badaboombox/SS-Handheld-Console/hardware/Comp Board/Audio.kicad_sch

## KiCad design hardware/Comp Board/Audio.kicad_sch (2026-07-28)

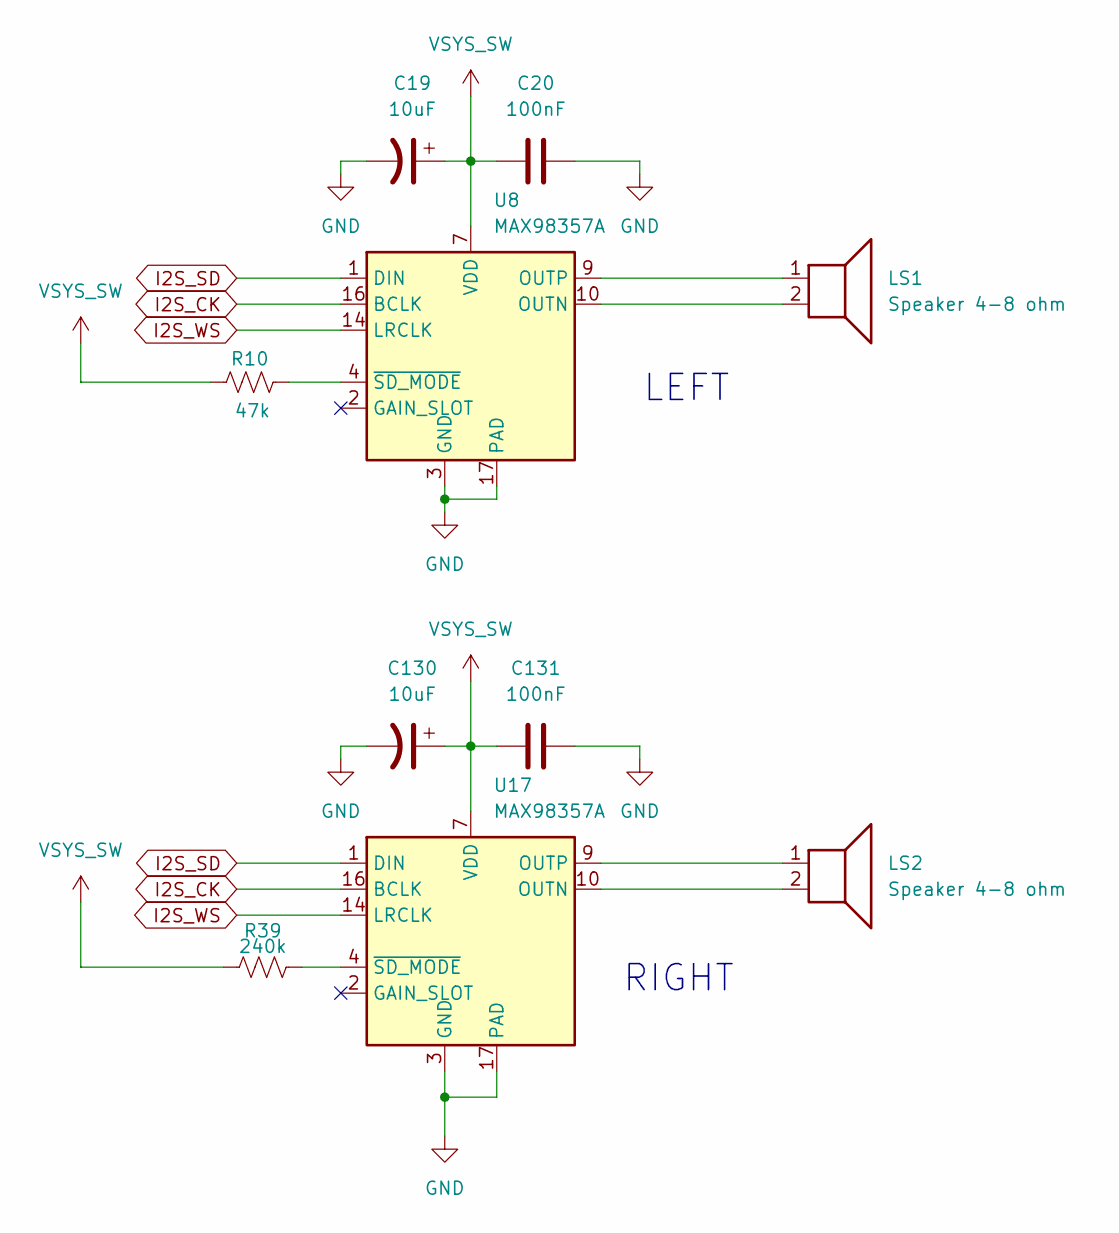
[picture p26: schematic Audio.kicad_sch]

Parts:
C19, C130: 10uF; C_0805_2012Metric
C20, C131: 100nF; C_0402_1005Metric
LS1, LS2: Speaker 4-8 ohm; TE_440054-2_1x02_P2.00mm_Vertical
R10: 47k; R_0402_1005Metric
R39: 240k; R_0402_1005Metric
U8, U17: MAX98357A; TQFN-16-1EP_3x3mm_P0.5mm_EP1.23x1.23mm

Connections:
GND: C19.2, C20.1, C130.2, C131.1, U8.3 (GND), U8.11 (GND), U8.15 (GND), U8.17 (PAD), U17.3 (GND), U17.11 (GND), U17.15 (GND), U17.17 (PAD)
I2S_CK: U8.16 (BCLK), U17.16 (BCLK)
I2S_SD: U8.1 (DIN), U17.1 (DIN)
I2S_WS: U8.14 (LRCLK), U17.14 (LRCLK)
unnamed: LS1.1, U8.9 (OUTP)
unnamed: LS1.2, U8.10 (OUTN)
unnamed: LS2.1, U17.9 (OUTP)
unnamed: LS2.2, U17.10 (OUTN)
unnamed: R10.2, U8.4 (~SD_MODE)
unnamed: R39.2, U17.4 (~SD_MODE)
VSYS_SW: C19.1, C20.2, C130.1, C131.2, R10.1, R39.1, U8.7 (VDD), U8.8 (VDD), U17.7 (VDD), U17.8 (VDD)

Notes on the sheet:
RIGHT
LEFT
