badaboombox/SS-Handheld-Console/hardware/Comp Board/CPU_CLK.kicad_sch

## KiCad design hardware/Comp Board/CPU_CLK.kicad_sch (2026-07-28)

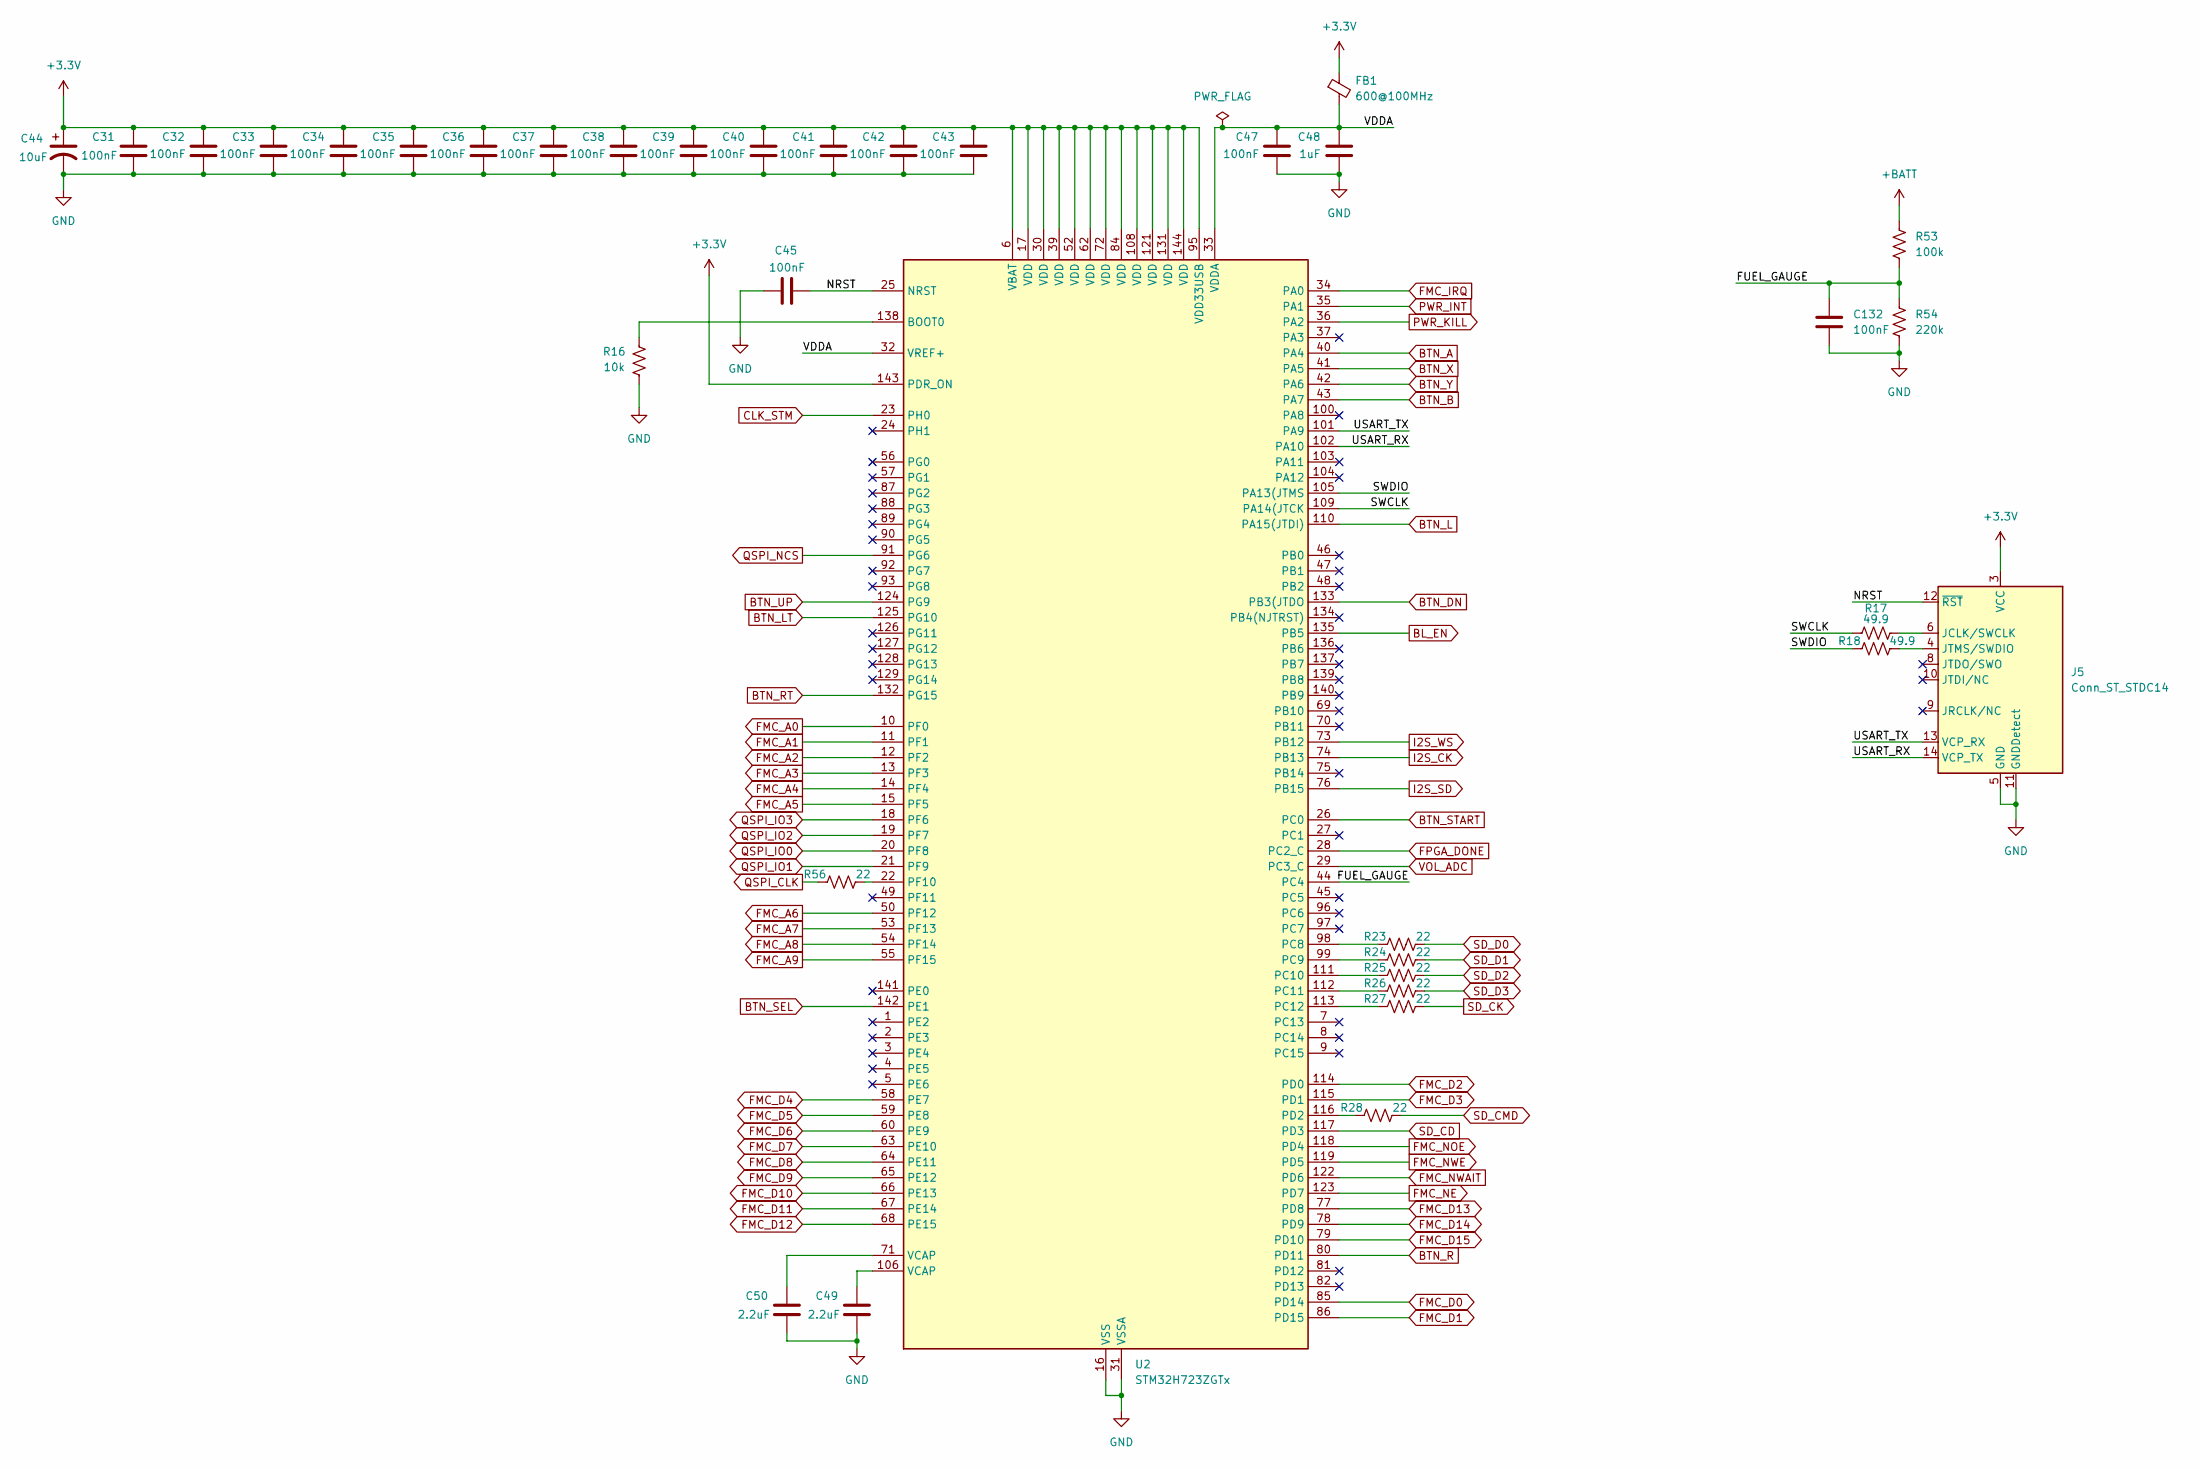
[picture p27: schematic CPU_CLK.kicad_sch]

Parts:
C31, C32, C33, C34, C35, C36, C37, C38, C39, C40, C41, C42, C43, C45, C47, C132: 100nF; C_0402_1005Metric
C44: 10uF; C_0805_2012Metric
C48: 1uF; C_0603_1608Metric
C49, C50: 2.2uF; C_0603_1608Metric
FB1: 600@100MHz; L_0805_2012Metric
J5: Conn_ST_STDC14; PinHeader_2x07_P1.27mm_Vertical
R16: 10k; R_0402_1005Metric
R17, R18: 49.9; R_0402_1005Metric
R23, R24, R25, R26, R27, R28, R56: 22; R_0402_1005Metric
R53: 100k; R_0402_1005Metric
R54: 220k; R_0402_1005Metric
U2: STM32H723ZGTx; LQFP-144_20x20mm_P0.5mm

Connections:
+3.3V: C31.1, C32.1, C33.1, C34.1, C35.1, C36.1, C37.1, C38.1, C39.1, C40.1, C41.1, C42.1, C43.1, C44.1, FB1.1, J5.3 (VCC), U2.6 (VBAT), U2.17 (VDD), U2.30 (VDD), U2.39 (VDD), U2.52 (VDD), U2.62 (VDD), U2.72 (VDD), U2.84 (VDD), U2.95 (VDD33USB), U2.108 (VDD), U2.121 (VDD), U2.131 (VDD), U2.143 (PDR_ON), U2.144 (VDD)
+BATT: R53.1
BL_EN: U2.135 (PB5)
BTN_A: U2.40 (PA4)
BTN_B: U2.43 (PA7)
BTN_DN: U2.133 (PB3(JTDO)
BTN_L: U2.110 (PA15(JTDI))
BTN_LT: U2.125 (PG10)
BTN_R: U2.80 (PD11)
BTN_RT: U2.132 (PG15)
BTN_SEL: U2.142 (PE1)
BTN_START: U2.26 (PC0)
BTN_UP: U2.124 (PG9)
BTN_X: U2.41 (PA5)
BTN_Y: U2.42 (PA6)
CLK_STM: U2.23 (PH0)
FMC_A0: U2.10 (PF0)
FMC_A1: U2.11 (PF1)
FMC_A2: U2.12 (PF2)
FMC_A3: U2.13 (PF3)
FMC_A4: U2.14 (PF4)
FMC_A5: U2.15 (PF5)
FMC_A6: U2.50 (PF12)
FMC_A7: U2.53 (PF13)
FMC_A8: U2.54 (PF14)
FMC_A9: U2.55 (PF15)
FMC_D0: U2.85 (PD14)
FMC_D1: U2.86 (PD15)
FMC_D2: U2.114 (PD0)
FMC_D3: U2.115 (PD1)
FMC_D4: U2.58 (PE7)
FMC_D5: U2.59 (PE8)
FMC_D6: U2.60 (PE9)
FMC_D7: U2.63 (PE10)
FMC_D8: U2.64 (PE11)
FMC_D9: U2.65 (PE12)
FMC_D10: U2.66 (PE13)
FMC_D11: U2.67 (PE14)
FMC_D12: U2.68 (PE15)
FMC_D13: U2.77 (PD8)
FMC_D14: U2.78 (PD9)
FMC_D15: U2.79 (PD10)
FMC_IRQ: U2.34 (PA0)
FMC_NE: U2.123 (PD7)
FMC_NOE: U2.118 (PD4)
FMC_NWAIT: U2.122 (PD6)
FMC_NWE: U2.119 (PD5)
FPGA_DONE: U2.28 (PC2_C)
FUEL_GAUGE: C132.1, R53.2, R54.1, U2.44 (PC4)
GND: C31.2, C32.2, C33.2, C34.2, C35.2, C36.2, C37.2, C38.2, C39.2, C40.2, C41.2, C42.2, C43.2, C44.2, C45.1, C47.2, C48.2, C49.2, C50.2, C132.2, J5.5 (GND), J5.7 (GND), J5.11 (GNDDetect), R16.1, R54.2, U2.16 (VSS), U2.31 (VSSA), U2.38 (VSS), U2.51 (VSS), U2.61 (VSS), U2.83 (VSS), U2.94 (VSS), U2.107 (VSS), U2.120 (VSS), U2.130 (VSS)
I2S_CK: U2.74 (PB13)
I2S_SD: U2.76 (PB15)
I2S_WS: U2.73 (PB12)
NRST: C45.2, J5.12 (~RST), U2.25 (NRST)
unnamed: C49.1, U2.106 (VCAP)
unnamed: C50.1, U2.71 (VCAP)
unnamed: J5.4 (JTMS/SWDIO), R18.2
unnamed: J5.6 (JCLK/SWCLK), R17.2
unnamed: R16.2, U2.138 (BOOT0)
unnamed: R23.1, U2.98 (PC8)
unnamed: R24.1, U2.99 (PC9)
unnamed: R25.1, U2.111 (PC10)
unnamed: R26.1, U2.112 (PC11)
unnamed: R27.1, U2.113 (PC12)
unnamed: R28.1, U2.116 (PD2)
unnamed: R56.2, U2.22 (PF10)
PWR_INT: U2.35 (PA1)
PWR_KILL: U2.36 (PA2)
QSPI_CLK: R56.1
QSPI_IO0: U2.20 (PF8)
QSPI_IO1: U2.21 (PF9)
QSPI_IO2: U2.19 (PF7)
QSPI_IO3: U2.18 (PF6)
QSPI_NCS: U2.91 (PG6)
SD_CD: U2.117 (PD3)
SD_CK: R27.2
SD_CMD: R28.2
SD_D0: R23.2
SD_D1: R24.2
SD_D2: R25.2
SD_D3: R26.2
SWCLK: R17.1, U2.109 (PA14(JTCK)
SWDIO: R18.1, U2.105 (PA13(JTMS)
USART_RX: J5.14 (VCP_TX), U2.102 (PA10)
USART_TX: J5.13 (VCP_RX), U2.101 (PA9)
VDDA: C47.1, C48.1, FB1.2, U2.32 (VREF+), U2.33 (VDDA)
VOL_ADC: U2.29 (PC3_C)
