badaboombox/SS-Handheld-Console/hardware/Comp Board/FPGA_Core_Conf.kicad_sch

## KiCad design hardware/Comp Board/FPGA_Core_Conf.kicad_sch (2026-07-28)

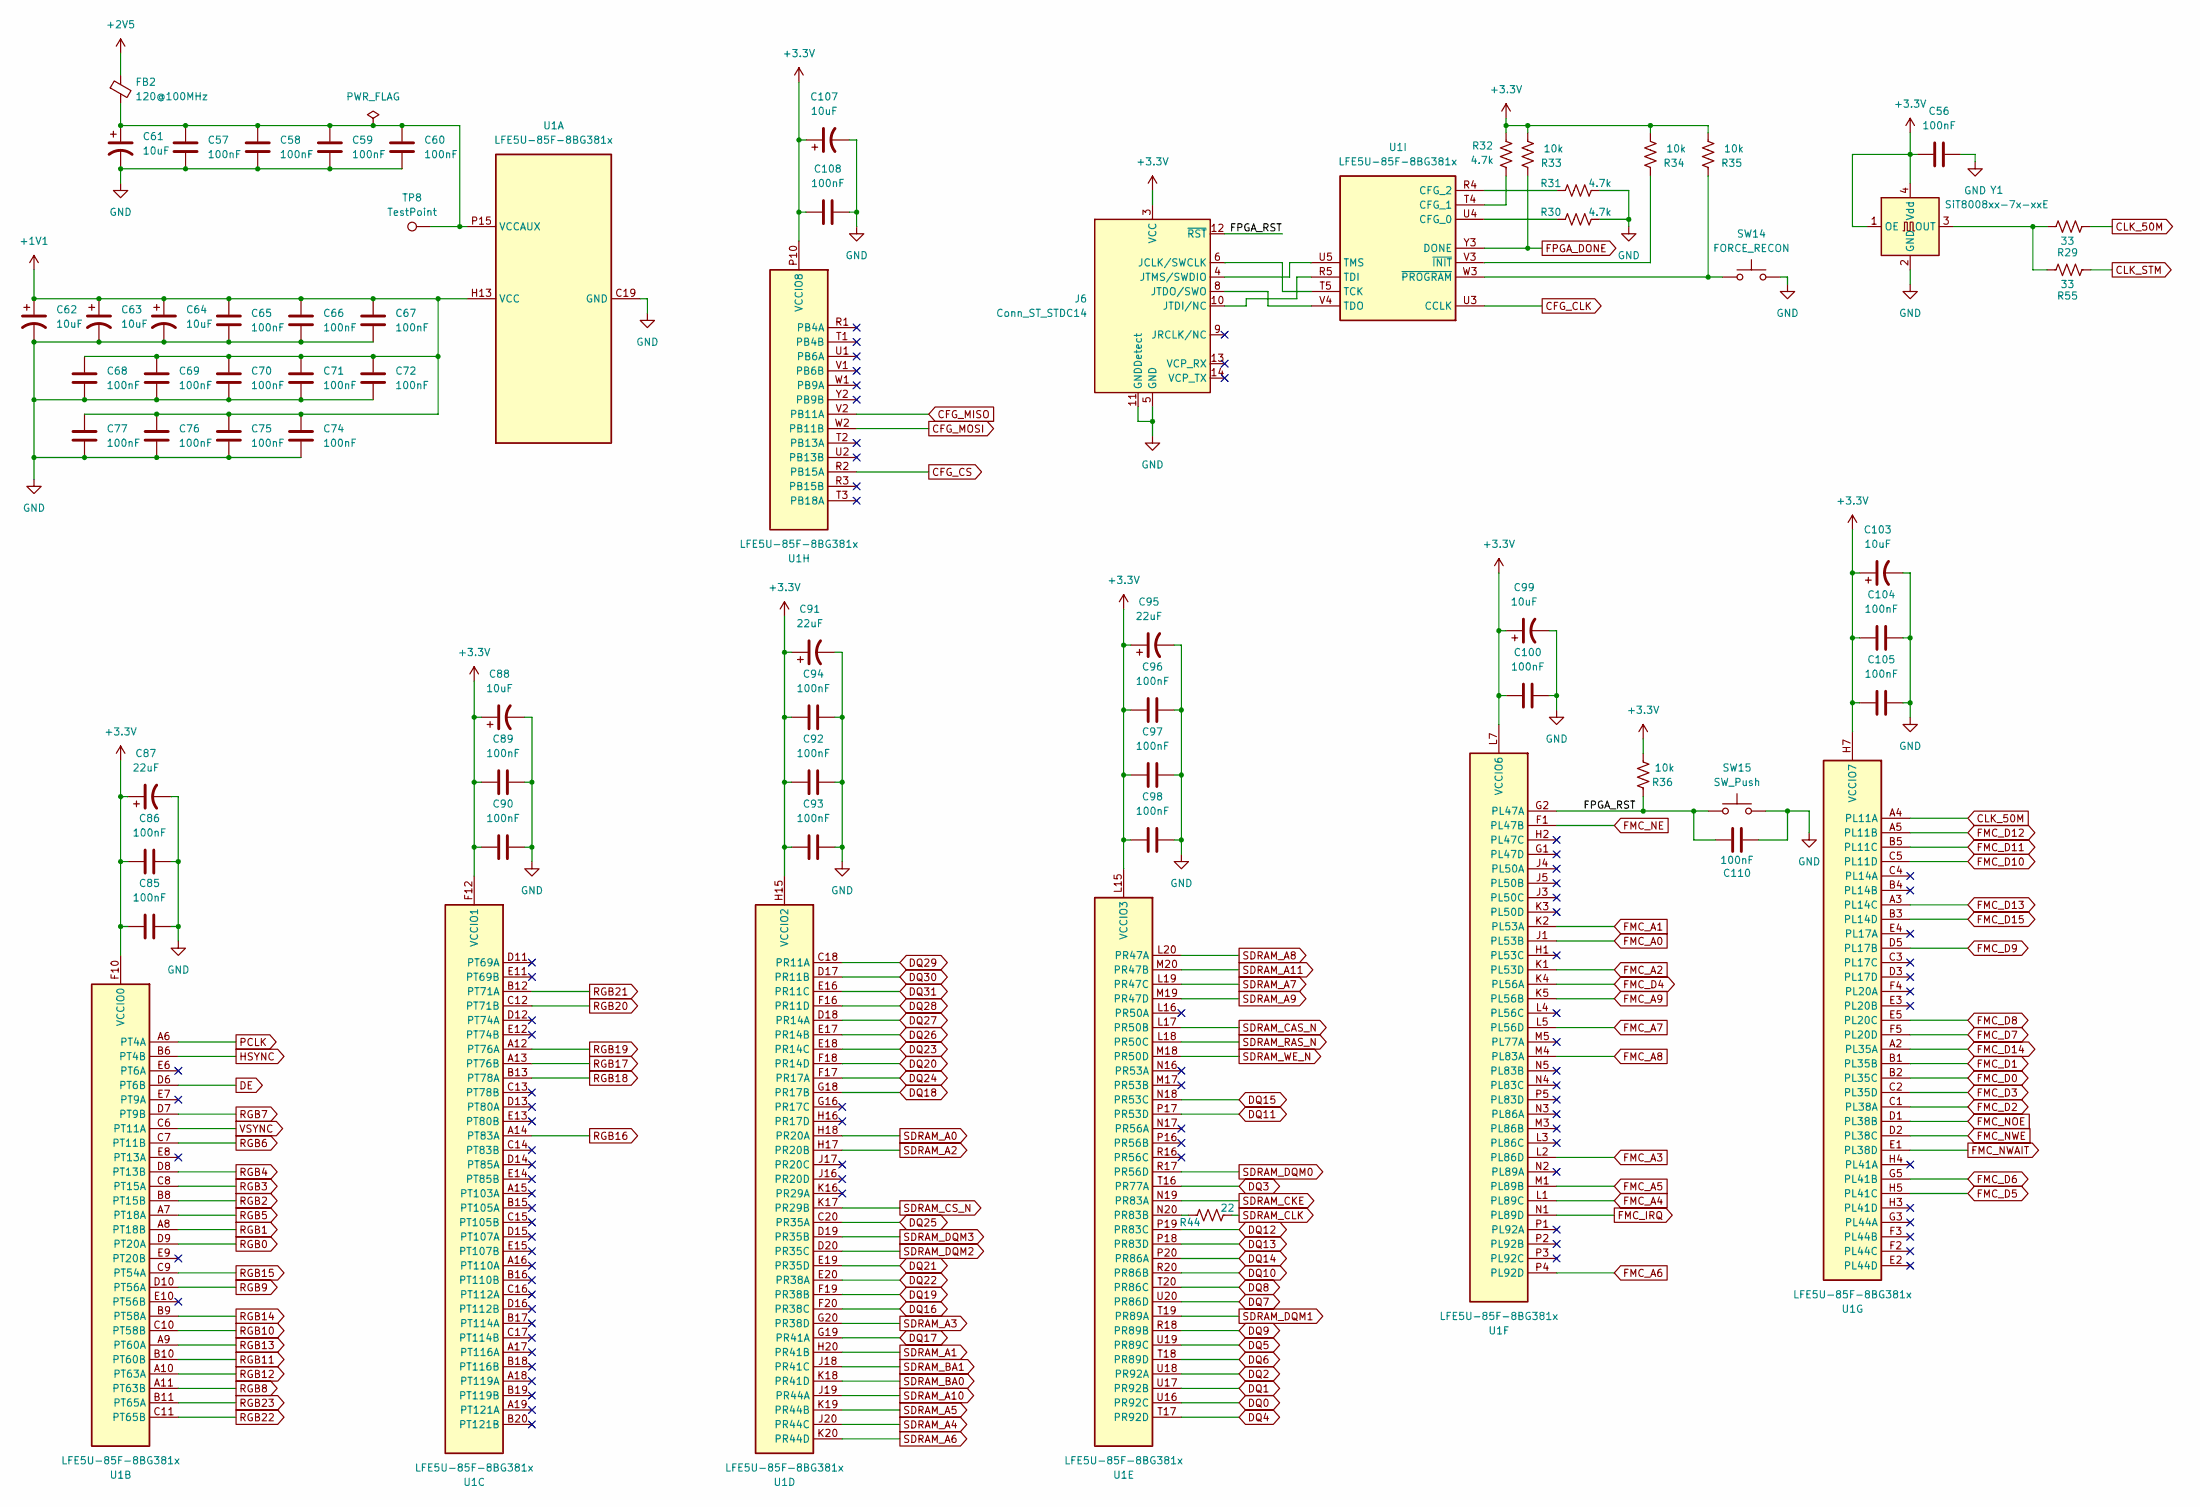
[picture p28: schematic FPGA_Core_Conf.kicad_sch]

Parts:
C56, C57, C58, C59, C60, C65, C66, C67, C68, C69, C70, C71, C72, C74, C75, C76, C77, C85, C86, C89, C90, C92, C93, C94, C96, C97, C98, C100, C104, C105, C108, C110: 100nF; C_0402_1005Metric
C61, C62, C63, C64, C88, C99, C103, C107: 10uF; C_0805_2012Metric
C87, C91, C95: 22uF; C_0805_2012Metric
FB2: 120@100MHz; L_0805_2012Metric
J6: Conn_ST_STDC14; PinHeader_2x07_P1.27mm_Vertical
R29, R55: 33; R_0402_1005Metric
R30, R31, R32: 4.7k; R_0402_1005Metric
R33, R34, R35, R36: 10k; R_0402_1005Metric
R44: 22; R_0402_1005Metric
SW14: FORCE_RECON; SW_Push_SPST_NO_Alps_SKRK
SW15: SW_Push; SW_Push_SPST_NO_Alps_SKRK
TP8: TestPoint; TestPoint_Pad_1.5x1.5mm
U1: LFE5U-85F-8BG381x; Lattice_caBGA-381_17x17mm_Layout20x20_P0.8mm
Y1: SiT8008xx-7x-xxE; Oscillator_SMD_SiT_PQFN-4Pin_2.0x1.6mm

Connections:
+1V1: C62.1, C63.1, C64.1, C65.2, C66.2, C67.2, C68.2, C69.2, C70.2, C71.2, C72.2, C74.2, C75.2, C76.2, C77.2, U1.H8 (VCC), U1.H9 (VCC), U1.H10 (VCC), U1.H11 (VCC), U1.H12 (VCC), U1.H13 (VCC), U1.J8 (VCC), U1.J13 (VCC), U1.K8 (VCC), U1.K13 (VCC), U1.L8 (VCC), U1.L13 (VCC), U1.M8 (VCC), U1.M13 (VCC), U1.N8 (VCC), U1.N9 (VCC), U1.N10 (VCC), U1.N11 (VCC), U1.N12 (VCC), U1.N13 (VCC)
+2V5: FB2.1
+3.3V: C56.1, C85.2, C86.2, C87.1, C88.1, C89.2, C90.2, C91.1, C92.2, C93.2, C94.2, C95.1, C96.2, C97.2, C98.2, C99.1, C100.2, C103.1, C104.2, C105.2, C107.1, C108.2, J6.3 (VCC), R32.1, R33.2, R34.2, R35.2, R36.2, U1.F9 (VCCIO0), U1.F10 (VCCIO0), U1.F11 (VCCIO1), U1.F12 (VCCIO1), U1.H6 (VCCIO7), U1.H7 (VCCIO7), U1.H14 (VCCIO2), U1.H15 (VCCIO2), U1.J6 (VCCIO7), U1.J15 (VCCIO2), U1.L6 (VCCIO6), U1.L7 (VCCIO6), U1.L14 (VCCIO3), U1.L15 (VCCIO3), U1.M6 (VCCIO6), U1.M15 (VCCIO3), U1.P9 (VCCIO8), U1.P10 (VCCIO8), Y1.1 (OE), Y1.4 (Vdd)
CFG_CLK: U1.U3 (CCLK)
CFG_CS: U1.R2 (PB15A)
CFG_MISO: U1.V2 (PB11A)
CFG_MOSI: U1.W2 (PB11B)
CLK_50M: R29.2, U1.A4 (PL11A)
CLK_STM: R55.2
DE: U1.D6 (PT6B)
DQ0: U1.U16 (PR92C)
DQ1: U1.U17 (PR92B)
DQ2: U1.U18 (PR92A)
DQ3: U1.T16 (PR77A)
DQ4: U1.T17 (PR92D)
DQ5: U1.U19 (PR89C)
DQ6: U1.T18 (PR89D)
DQ7: U1.U20 (PR86D)
DQ8: U1.T20 (PR86C)
DQ9: U1.R18 (PR89B)
DQ10: U1.R20 (PR86B)
DQ11: U1.P17 (PR53D)
DQ12: U1.P19 (PR83C)
DQ13: U1.P18 (PR83D)
DQ14: U1.P20 (PR86A)
DQ15: U1.N18 (PR53C)
DQ16: U1.F20 (PR38C)
DQ17: U1.G19 (PR41A)
DQ18: U1.G18 (PR17B)
DQ19: U1.F19 (PR38B)
DQ20: U1.F18 (PR14D)
DQ21: U1.E19 (PR35D)
DQ22: U1.E20 (PR38A)
DQ23: U1.E18 (PR14C)
DQ24: U1.F17 (PR17A)
DQ25: U1.C20 (PR35A)
DQ26: U1.E17 (PR14B)
DQ27: U1.D18 (PR14A)
DQ28: U1.F16 (PR11D)
DQ29: U1.C18 (PR11A)
DQ30: U1.D17 (PR11B)
DQ31: U1.E16 (PR11C)
FMC_A0: U1.J1 (PL53B)
FMC_A1: U1.K2 (PL53A)
FMC_A2: U1.K1 (PL53D)
FMC_A3: U1.L2 (PL86D)
FMC_A4: U1.L1 (PL89C)
FMC_A5: U1.M1 (PL89B)
FMC_A6: U1.P4 (PL92D)
FMC_A7: U1.L5 (PL56D)
FMC_A8: U1.M4 (PL83A)
FMC_A9: U1.K5 (PL56B)
FMC_D0: U1.B2 (PL35C)
FMC_D1: U1.B1 (PL35B)
FMC_D2: U1.C1 (PL38A)
FMC_D3: U1.C2 (PL35D)
FMC_D4: U1.K4 (PL56A)
FMC_D5: U1.H5 (PL41C)
FMC_D6: U1.G5 (PL41B)
FMC_D7: U1.F5 (PL20D)
FMC_D8: U1.E5 (PL20C)
FMC_D9: U1.D5 (PL17B)
FMC_D10: U1.C5 (PL11D)
FMC_D11: U1.B5 (PL11C)
FMC_D12: U1.A5 (PL11B)
FMC_D13: U1.A3 (PL14C)
FMC_D14: U1.A2 (PL35A)
FMC_D15: U1.B3 (PL14D)
FMC_IRQ: U1.N1 (PL89D)
FMC_NE: U1.F1 (PL47B)
FMC_NOE: U1.D1 (PL38B)
FMC_NWAIT: U1.E1 (PL38D)
FMC_NWE: U1.D2 (PL38C)
FPGA_DONE: R33.1, U1.Y3 (DONE)
FPGA_RST: C110.2, J6.12 (~RST), R36.1, SW15.1, U1.G2 (PL47A)
GND: C56.2, C57.1, C58.1, C59.1, C60.1, C61.2, C62.2, C63.2, C64.2, C65.1, C66.1, C67.1, C68.1, C69.1, C70.1, C71.1, C72.1, C74.1, C75.1, C76.1, C77.1, C85.1, C86.1, C87.2, C88.2, C89.1, C90.1, C91.2, C92.1, C93.1, C94.1, C95.2, C96.1, C97.1, C98.1, C99.2, C100.1, C103.2, C104.1, C105.1, C107.2, C108.1, C110.1, J6.5 (GND), J6.7 (GND), J6.11 (GNDDetect), R30.2, R31.2, SW14.2, SW15.2, U1.B7 (GND), U1.B14 (GND), U1.C19 (GND), U1.D4 (GND), U1.F7 (GND), U1.F8 (GND), U1.F13 (GND), U1.F14 (GND), U1.G4 (GND), U1.G6 (GND), U1.G7 (GND), U1.G8 (GND), U1.G9 (GND), U1.G10 (GND), U1.G11 (GND), U1.G12 (GND), U1.G13 (GND), U1.G14 (GND), U1.G15 (GND), U1.G17 (GND), U1.H19 (GND), U1.J2 (GND), U1.J7 (GND), U1.J9 (GND), U1.J10 (GND), U1.J11 (GND), U1.J12 (GND), U1.J14 (GND), U1.K6 (GND), U1.K7 (GND), U1.K9 (GND), U1.K10 (GND), U1.K11 (GND), U1.K12 (GND), U1.K14 (GND), U1.K15 (GND), U1.L9 (GND), U1.L10 (GND), U1.L11 (GND), U1.L12 (GND), U1.M2 (GND), U1.M7 (GND), U1.M9 (GND), U1.M10 (GND), U1.M11 (GND), U1.M12 (GND), U1.M14 (GND), U1.M16 (GND), U1.N6 (GND), U1.N7 (GND), U1.N14 (GND), U1.N15 (GND), U1.P7 (GND), U1.P8 (GND), U1.P11 (GND), U1.P12 (GND), U1.P13 (GND), U1.P14 (GND), U1.R19 (GND), U1.T6 (GND), U1.T7 (GND), U1.T8 (GND), U1.T9 (GND), U1.T10 (GND), U1.T11 (GND), U1.T12 (GND), U1.T13 (GND), U1.T14 (GND), U1.T15 (GND), U1.U6 (GND), U1.U7 (GND), U1.U8 (GND), U1.U9 (GND), U1.U10 (GND), U1.U11 (GND), U1.U12 (GND), U1.U13 (GND), U1.U14 (GND), U1.U15 (GND), U1.V5 (GND), U1.V6 (GND), U1.V7 (GND), U1.V8 (GND), U1.V9 (GND), U1.V10 (GND), U1.V11 (GND), U1.V12 (GND), U1.V13 (GND), U1.V14 (GND), U1.V15 (GND), U1.V16 (GND), U1.V17 (GND), U1.V18 (GND), U1.V19 (GND), U1.V20 (GND), U1.W6 (GND), U1.W7 (GND), U1.W12 (GND), U1.W15 (GND), U1.W16 (GND), U1.W19 (GND), U1.W20 (GND), U1.Y5 (GND), U1.Y6 (GND), U1.Y7 (GND), U1.Y8 (GND), U1.Y11 (GND), U1.Y12 (GND), U1.Y14 (GND), U1.Y15 (GND), U1.Y16 (GND), U1.Y17 (GND), U1.Y19 (GND), Y1.2 (GND)
HSYNC: U1.B6 (PT4B)
unnamed: C57.2, C58.2, C59.2, C60.2, C61.1, FB2.2, TP8.1, U1.F6 (VCCAUX), U1.F15 (VCCAUX), U1.P6 (VCCAUX), U1.P15 (VCCAUX)
unnamed: J6.4 (JTMS/SWDIO), U1.U5 (TMS)
unnamed: J6.6 (JCLK/SWCLK), U1.T5 (TCK)
unnamed: J6.8 (JTDO/SWO), U1.V4 (TDO)
unnamed: J6.10 (JTDI/NC), U1.R5 (TDI)
unnamed: R29.1, R55.1, Y1.3 (OUT)
unnamed: R30.1, U1.U4 (CFG_0)
unnamed: R31.1, U1.R4 (CFG_2)
unnamed: R32.2, U1.T4 (CFG_1)
unnamed: R34.1, U1.V3 (~INIT)
unnamed: R35.1, SW14.1, U1.W3 (~PROGRAM)
unnamed: R44.1, U1.N20 (PR83B)
PCLK: U1.A6 (PT4A)
RGB0: U1.D9 (PT20A)
RGB1: U1.A8 (PT18B)
RGB2: U1.B8 (PT15B)
RGB3: U1.C8 (PT15A)
RGB4: U1.D8 (PT13B)
RGB5: U1.A7 (PT18A)
RGB6: U1.C7 (PT11B)
RGB7: U1.D7 (PT9B)
RGB8: U1.A11 (PT63B)
RGB9: U1.D10 (PT56A)
RGB10: U1.C10 (PT58B)
RGB11: U1.B10 (PT60B)
RGB12: U1.A10 (PT63A)
RGB13: U1.A9 (PT60A)
RGB14: U1.B9 (PT58A)
RGB15: U1.C9 (PT54A)
RGB16: U1.A14 (PT83A)
RGB17: U1.A13 (PT76B)
RGB18: U1.B13 (PT78A)
RGB19: U1.A12 (PT76A)
RGB20: U1.C12 (PT71B)
RGB21: U1.B12 (PT71A)
RGB22: U1.C11 (PT65B)
RGB23: U1.B11 (PT65A)
SDRAM_A0: U1.H18 (PR20A)
SDRAM_A1: U1.H20 (PR41B)
SDRAM_A2: U1.H17 (PR20B)
SDRAM_A3: U1.G20 (PR38D)
SDRAM_A4: U1.J20 (PR44C)
SDRAM_A5: U1.K19 (PR44B)
SDRAM_A6: U1.K20 (PR44D)
SDRAM_A7: U1.L19 (PR47C)
SDRAM_A8: U1.L20 (PR47A)
SDRAM_A9: U1.M19 (PR47D)
SDRAM_A10: U1.J19 (PR44A)
SDRAM_A11: U1.M20 (PR47B)
SDRAM_BA0: U1.K18 (PR41D)
SDRAM_BA1: U1.J18 (PR41C)
SDRAM_CAS_N: U1.L17 (PR50B)
SDRAM_CKE: U1.N19 (PR83A)
SDRAM_CLK: R44.2
SDRAM_CS_N: U1.K17 (PR29B)
SDRAM_DQM0: U1.R17 (PR56D)
SDRAM_DQM1: U1.T19 (PR89A)
SDRAM_DQM2: U1.D20 (PR35C)
SDRAM_DQM3: U1.D19 (PR35B)
SDRAM_RAS_N: U1.L18 (PR50C)
SDRAM_WE_N: U1.M18 (PR50D)
VSYNC: U1.C6 (PT11A)
