badaboombox/SS-Handheld-Console/hardware/Comp Board/PSRAM_SD.kicad_sch

## KiCad design hardware/Comp Board/PSRAM_SD.kicad_sch (2026-07-28)

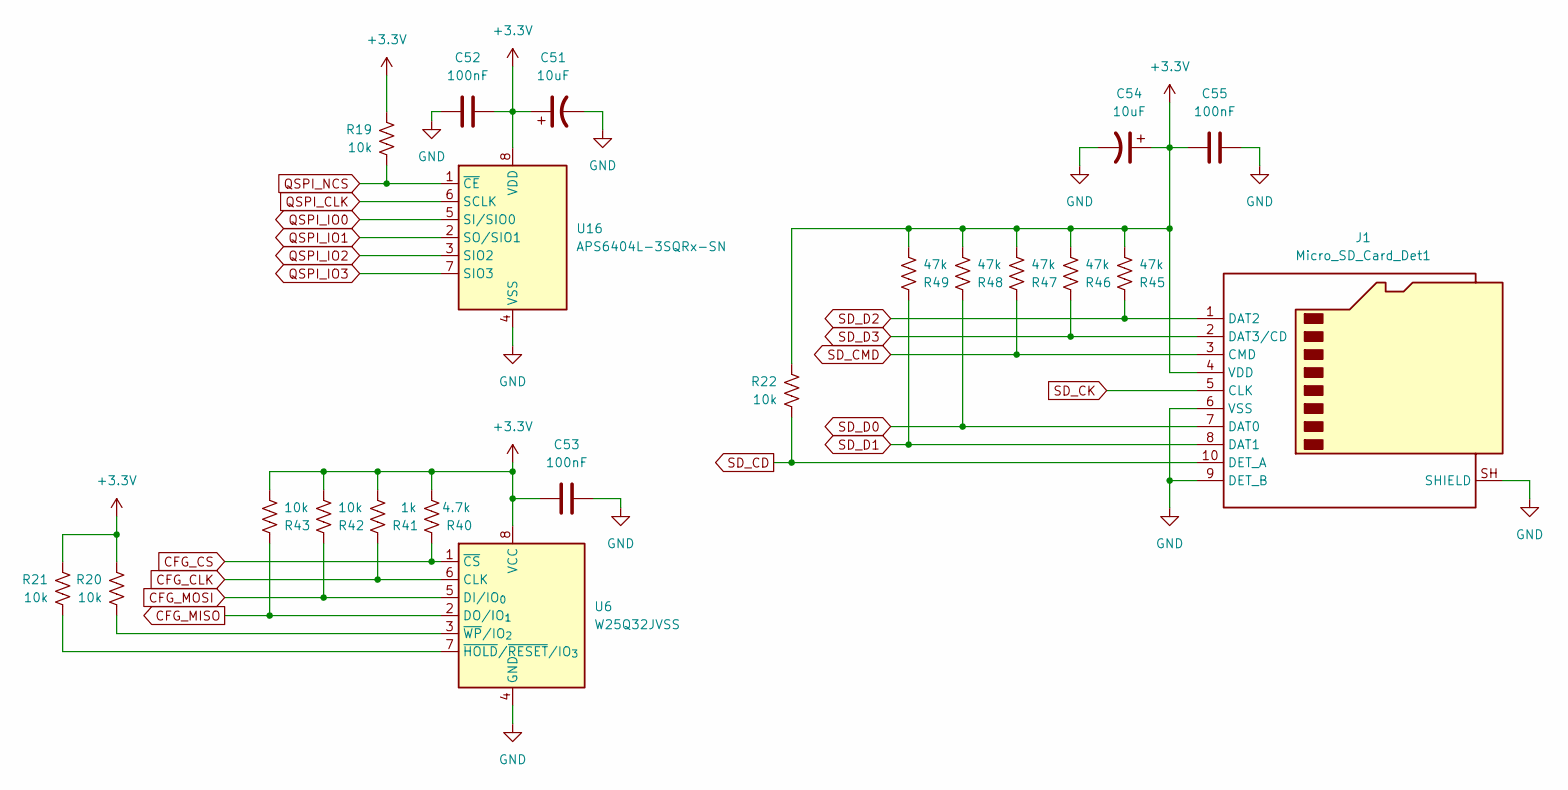
[picture p29: schematic PSRAM_SD.kicad_sch]

Parts:
C51, C54: 10uF; C_0805_2012Metric
C52, C53, C55: 100nF; C_0402_1005Metric
J1: Micro_SD_Card_Det1; microSD_HC_Hirose_DM3D-SF
R19, R20, R21, R22, R42, R43: 10k; R_0402_1005Metric
R40: 4.7k; R_0402_1005Metric
R41: 1k; R_0402_1005Metric
R45, R46, R47, R48, R49: 47k; R_0402_1005Metric
U6: W25Q32JVSS; SOIC-8_5.3x5.3mm_P1.27mm
U16: APS6404L-3SQRx-SN; SOIC-8_3.9x4.9mm_P1.27mm

Connections:
+3.3V: C51.1, C52.2, C53.1, C54.1, C55.2, J1.4 (VDD), R19.1, R20.1, R21.1, R22.1, R40.2, R41.2, R42.2, R43.2, R45.2, R46.2, R47.2, R48.2, R49.2, U6.8 (VCC), U16.8 (VDD)
CFG_CLK: R41.1, U6.6 (CLK)
CFG_CS: R40.1, U6.1 (~CS)
CFG_MISO: R43.1, U6.2 (DO/IO_{1})
CFG_MOSI: R42.1, U6.5 (DI/IO_{0})
GND: C51.2, C52.1, C53.2, C54.2, C55.1, J1.6 (VSS), J1.9 (DET_B), J1.SH (SHIELD), U6.4 (GND), U16.4 (VSS)
unnamed: R20.2, U6.3 (~WP/IO_{2})
unnamed: R21.2, U6.7 (~HOLD/~RESET/IO_{3})
QSPI_CLK: U16.6 (SCLK)
QSPI_IO0: U16.5 (SI/SIO0)
QSPI_IO1: U16.2 (SO/SIO1)
QSPI_IO2: U16.3 (SIO2)
QSPI_IO3: U16.7 (SIO3)
QSPI_NCS: R19.2, U16.1 (~CE)
SD_CD: J1.10 (DET_A), R22.2
SD_CK: J1.5 (CLK)
SD_CMD: J1.3 (CMD), R47.1
SD_D0: J1.7 (DAT0), R48.1
SD_D1: J1.8 (DAT1), R49.1
SD_D2: J1.1 (DAT2), R45.1
SD_D3: J1.2 (DAT3/CD), R46.1
