badaboombox/SS-Handheld-Console/hardware/Comp Board/PWR.kicad_sch

## KiCad design hardware/Comp Board/PWR.kicad_sch (2026-07-28)

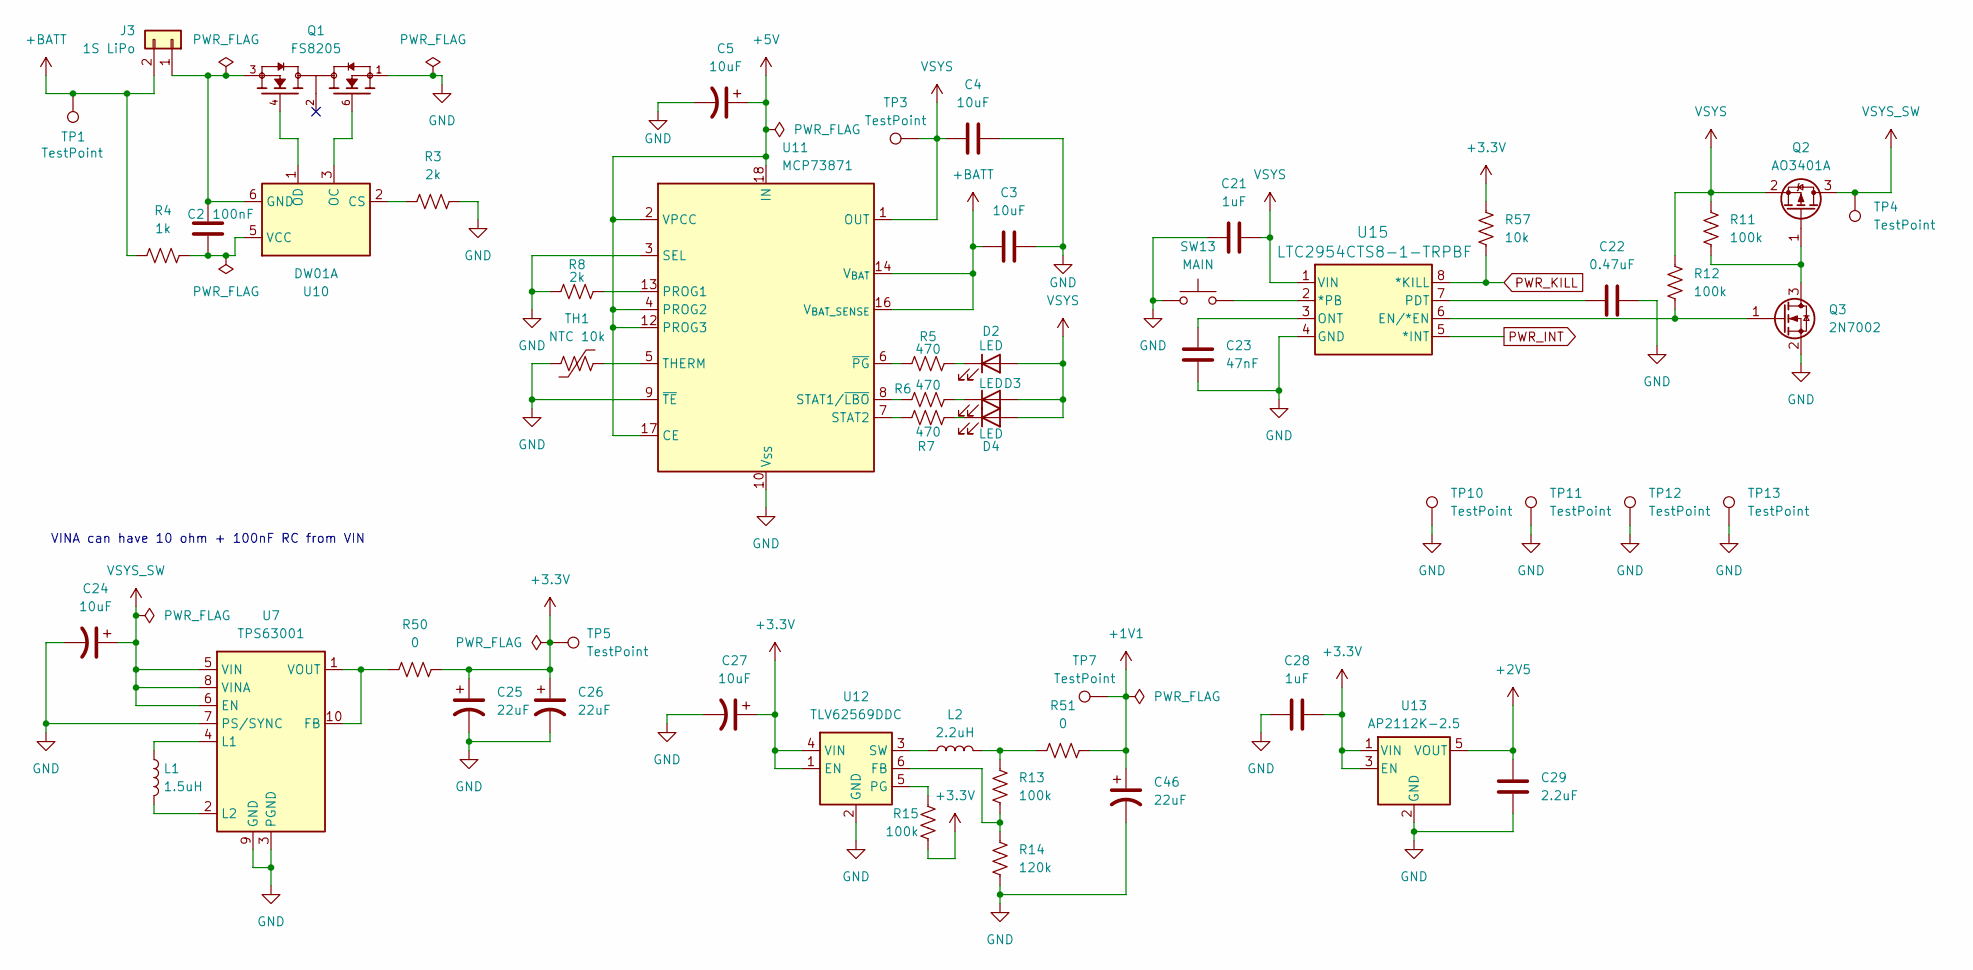
[picture p30: schematic PWR.kicad_sch]

Parts:
C2: 100nF; C_0402_1005Metric
C3, C4, C5, C24, C27: 10uF; C_0805_2012Metric
C21, C28: 1uF; C_0603_1608Metric
C22: 0.47uF; C_0402_1005Metric
C23: 47nF; C_0402_1005Metric
C25, C26, C46: 22uF; C_0805_2012Metric
C29: 2.2uF; C_0603_1608Metric
D2, D3, D4: LED; LED_0603_1608Metric
J3: 1S LiPo; JST_PH_B2B-PH-K_1x02_P2.00mm_Vertical
L1: 1.5uH; L_1008_2520Metric
L2: 2.2uH; L_1008_2520Metric
Q1: FS8205; SOT-23-6; PARTREV 1.9
Q2: AO3401A; SOT-23
Q3: 2N7002; SOT-23
R3, R8: 2k; R_0402_1005Metric
R4: 1k; R_0402_1005Metric
R5, R6, R7: 470; R_0402_1005Metric
R11, R12, R13, R15: 100k; R_0402_1005Metric
R14: 120k; R_0402_1005Metric
R50, R51: 0; R_1206_3216Metric
R57: 10k; R_0402_1005Metric
SW13: MAIN; SW_SPST_SKQG_WithStem
TH1: NTC 10k; R_0603_1608Metric
TP1, TP3, TP4, TP5, TP7: TestPoint; TestPoint_Pad_1.5x1.5mm
TP10, TP11, TP12, TP13: TestPoint; TestPoint_THTPad_1.5x1.5mm_Drill0.7mm
U7: TPS63001; Texas_DRC0010J_ThermalVias
U10: DW01A; SOT-23-6
U11: MCP73871; QFN-20-1EP_4x4mm_P0.5mm_EP2.5x2.5mm
U12: TLV62569DDC; SOT-23-6
U13: AP2112K-2.5; SOT-23-5
U15: LTC2954CTS8-1-TRPBF; TSOT-23-8

Connections:
+1V1: C46.1, R51.2, TP7.1
+2V5: C29.2, U13.5 (VOUT)
+3.3V: C25.1, C26.1, C27.1, C28.2, R15.1, R50.2, R57.1, TP5.1, U12.1 (EN), U12.4 (VIN), U13.1 (VIN), U13.3 (EN)
+5V: C5.1, U11.2 (VPCC), U11.4 (PROG2), U11.12 (PROG3), U11.17 (CE), U11.18 (IN), U11.19 (IN)
+BATT: C3.1, J3.2, R4.1, TP1.1, U11.14 (V_{BAT}), U11.15 (V_{BAT}), U11.16 (V_{BAT_SENSE})
GND: C3.2, C4.2, C5.2, C21.1, C22.2, C23.2, C24.2, C25.2, C26.2, C27.2, C28.1, C29.1, C46.2, Q1.1, Q3.2 (S), R3.2, R8.1, R14.2, SW13.1, TH1.1, TP10.1, TP11.1, TP12.1, TP13.1, U7.3 (PGND), U7.7 (PS/SYNC), U7.9 (GND), U7.11 (PGND), U11.3 (SEL), U11.9 (~TE), U11.10 (V_{SS}), U11.11 (V_{SS}), U11.21 (V_{SS}), U12.2 (GND), U13.2 (GND), U15.4 (GND)
unnamed: C2.1, J3.1, Q1.3, U10.6 (GND)
unnamed: C2.2, R4.2, U10.5 (VCC)
unnamed: C22.1, U15.7 (PDT)
unnamed: C23.1, U15.3 (ONT)
unnamed: D2.1 (K), R5.2
unnamed: D3.1 (K), R6.2
unnamed: D4.1 (K), R7.2
unnamed: L1.1, U7.4 (L1)
unnamed: L1.2, U7.2 (L2)
unnamed: L2.1, U12.3 (SW)
unnamed: L2.2, R13.1, R51.1
unnamed: Q1.2, Q1.5
unnamed: Q1.4, U10.1 (OD)
unnamed: Q1.6, U10.3 (OC)
unnamed: Q2.1 (G), Q3.3 (D), R11.1
unnamed: Q3.1 (G), R12.1, U15.6 (EN/*EN)
unnamed: R3.1, U10.2 (CS)
unnamed: R5.1, U11.6 (~PG)
unnamed: R6.1, U11.8 (STAT1/~LBO)
unnamed: R7.1, U11.7 (STAT2)
unnamed: R8.2, U11.13 (PROG1)
unnamed: R13.2, R14.1, U12.6 (FB)
unnamed: R15.2, U12.5 (PG)
unnamed: R50.1, U7.1 (VOUT), U7.10 (FB)
unnamed: SW13.2, U15.2 (*PB)
unnamed: TH1.2, U11.5 (THERM)
PWR_INT: U15.5 (*INT)
PWR_KILL: R57.2, U15.8 (*KILL)
VSYS: C4.1, C21.2, D2.2 (A), D3.2 (A), D4.2 (A), Q2.2 (S), R11.2, R12.2, TP3.1, U11.1 (OUT), U11.20 (OUT), U15.1 (VIN)
VSYS_SW: C24.1, Q2.3 (D), TP4.1, U7.5 (VIN), U7.6 (EN), U7.8 (VINA)

Notes on the sheet:
VINA can have 10 ohm + 100nF RC from VIN
