badaboombox/SS-Handheld-Console/hardware/Comp Board/Panel_BL.kicad_sch

## KiCad design hardware/Comp Board/Panel_BL.kicad_sch (2026-07-28)

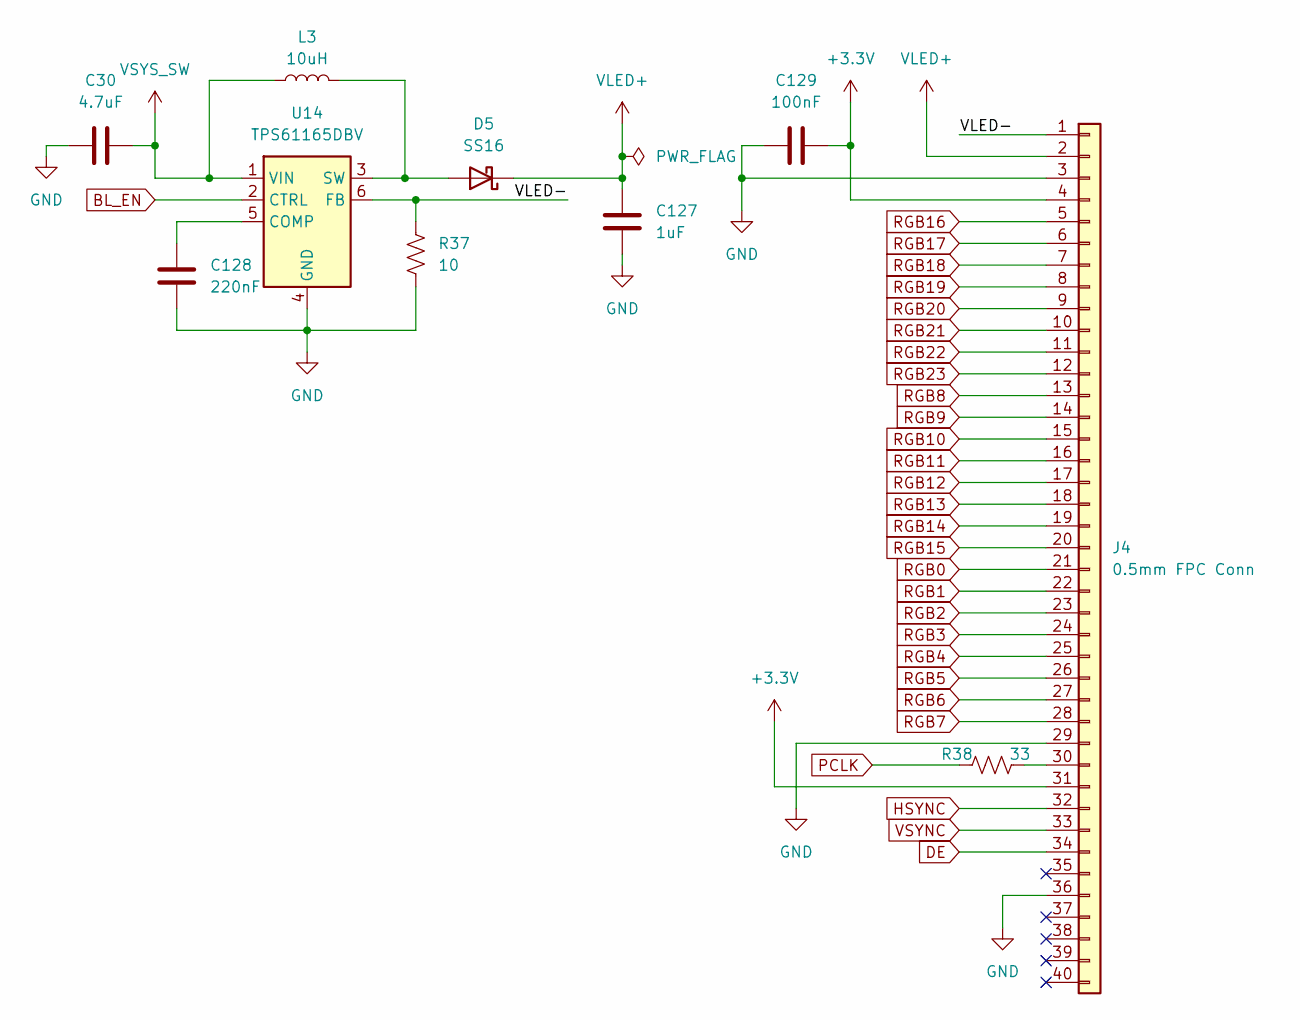
[picture p31: schematic Panel_BL.kicad_sch]

Parts:
C30: 4.7uF; C_0603_1608Metric
C127: 1uF; C_1206_3216Metric
C128: 220nF; C_0402_1005Metric
C129: 100nF; C_0402_1005Metric
D5: SS16; D_SMA
J4: 0.5mm FPC Conn; Hirose_FH12-40S-0.5SH_1x40-1MP_P0.50mm_Horizontal
L3: 10uH; L_Abracon_ASPI-4030S
R37: 10; R_0402_1005Metric
R38: 33; R_0402_1005Metric
U14: TPS61165DBV; SOT-23-6

Connections:
+3.3V: C129.2, J4.4, J4.31
BL_EN: U14.2 (CTRL)
DE: J4.34
GND: C30.2, C127.2, C128.2, C129.1, J4.3, J4.29, J4.36, R37.2, U14.4 (GND)
HSYNC: J4.32
unnamed: C128.1, U14.5 (COMP)
unnamed: D5.2 (A), L3.2, U14.3 (SW)
unnamed: J4.30, R38.2
PCLK: R38.1
RGB0: J4.21
RGB1: J4.22
RGB2: J4.23
RGB3: J4.24
RGB4: J4.25
RGB5: J4.26
RGB6: J4.27
RGB7: J4.28
RGB8: J4.13
RGB9: J4.14
RGB10: J4.15
RGB11: J4.16
RGB12: J4.17
RGB13: J4.18
RGB14: J4.19
RGB15: J4.20
RGB16: J4.5
RGB17: J4.6
RGB18: J4.7
RGB19: J4.8
RGB20: J4.9
RGB21: J4.10
RGB22: J4.11
RGB23: J4.12
VLED+: C127.1, D5.1 (K), J4.2
VLED-: J4.1, R37.1, U14.6 (FB)
VSYNC: J4.33
VSYS_SW: C30.1, L3.1, U14.1 (VIN)
