badaboombox/SS-Handheld-Console/hardware/Comp Board/SDRAM.kicad_sch

## KiCad design hardware/Comp Board/SDRAM.kicad_sch (2026-07-28)

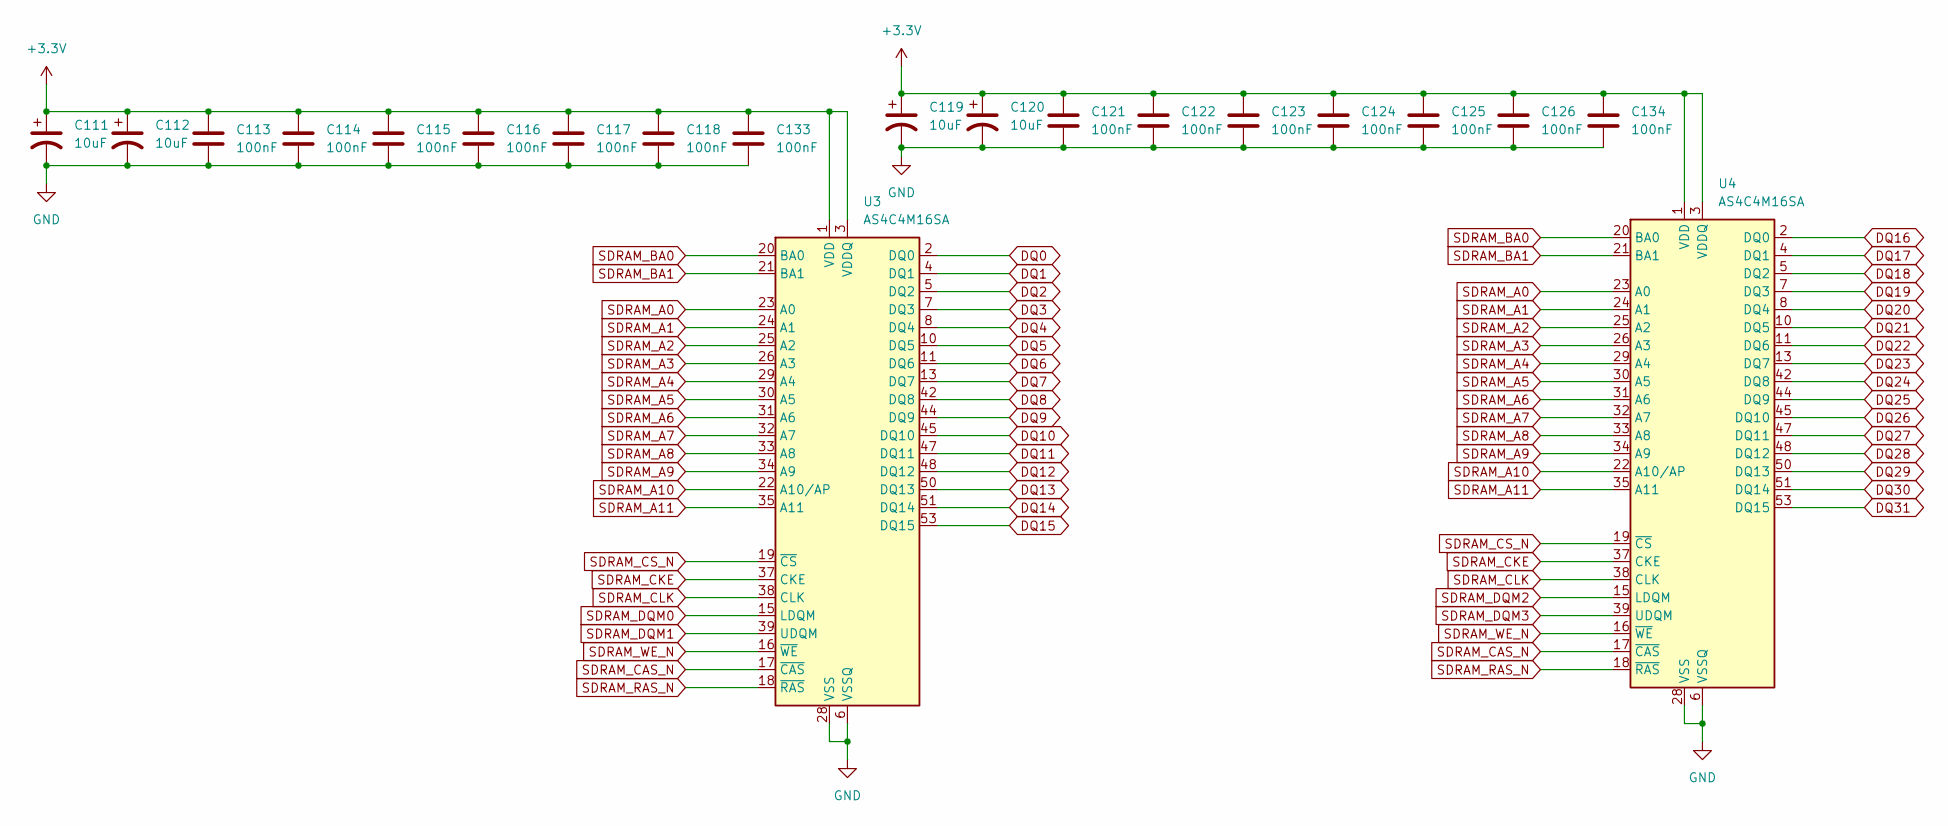
[picture p32: schematic SDRAM.kicad_sch]

Parts:
C111, C112, C119, C120: 10uF; C_0805_2012Metric
C113, C114, C115, C116, C117, C118, C121, C122, C123, C124, C125, C126, C133, C134: 100nF; C_0402_1005Metric
U3, U4: AS4C4M16SA; TSOP-II-54_22.2x10.16mm_P0.8mm

Connections:
+3.3V: C111.1, C112.1, C113.2, C114.2, C115.2, C116.2, C117.2, C118.2, C119.1, C120.1, C121.2, C122.2, C123.2, C124.2, C125.2, C126.2, C133.2, C134.2, U3.1 (VDD), U3.3 (VDDQ), U3.9 (VDDQ), U3.14 (VDD), U3.27 (VDD), U3.43 (VDDQ), U3.49 (VDDQ), U4.1 (VDD), U4.3 (VDDQ), U4.9 (VDDQ), U4.14 (VDD), U4.27 (VDD), U4.43 (VDDQ), U4.49 (VDDQ)
DQ0: U3.2 (DQ0)
DQ1: U3.4 (DQ1)
DQ2: U3.5 (DQ2)
DQ3: U3.7 (DQ3)
DQ4: U3.8 (DQ4)
DQ5: U3.10 (DQ5)
DQ6: U3.11 (DQ6)
DQ7: U3.13 (DQ7)
DQ8: U3.42 (DQ8)
DQ9: U3.44 (DQ9)
DQ10: U3.45 (DQ10)
DQ11: U3.47 (DQ11)
DQ12: U3.48 (DQ12)
DQ13: U3.50 (DQ13)
DQ14: U3.51 (DQ14)
DQ15: U3.53 (DQ15)
DQ16: U4.2 (DQ0)
DQ17: U4.4 (DQ1)
DQ18: U4.5 (DQ2)
DQ19: U4.7 (DQ3)
DQ20: U4.8 (DQ4)
DQ21: U4.10 (DQ5)
DQ22: U4.11 (DQ6)
DQ23: U4.13 (DQ7)
DQ24: U4.42 (DQ8)
DQ25: U4.44 (DQ9)
DQ26: U4.45 (DQ10)
DQ27: U4.47 (DQ11)
DQ28: U4.48 (DQ12)
DQ29: U4.50 (DQ13)
DQ30: U4.51 (DQ14)
DQ31: U4.53 (DQ15)
GND: C111.2, C112.2, C113.1, C114.1, C115.1, C116.1, C117.1, C118.1, C119.2, C120.2, C121.1, C122.1, C123.1, C124.1, C125.1, C126.1, C133.1, C134.1, U3.6 (VSSQ), U3.12 (VSSQ), U3.28 (VSS), U3.41 (VSS), U3.46 (VSSQ), U3.52 (VSSQ), U3.54 (VSS), U4.6 (VSSQ), U4.12 (VSSQ), U4.28 (VSS), U4.41 (VSS), U4.46 (VSSQ), U4.52 (VSSQ), U4.54 (VSS)
SDRAM_A0: U3.23 (A0), U4.23 (A0)
SDRAM_A1: U3.24 (A1), U4.24 (A1)
SDRAM_A2: U3.25 (A2), U4.25 (A2)
SDRAM_A3: U3.26 (A3), U4.26 (A3)
SDRAM_A4: U3.29 (A4), U4.29 (A4)
SDRAM_A5: U3.30 (A5), U4.30 (A5)
SDRAM_A6: U3.31 (A6), U4.31 (A6)
SDRAM_A7: U3.32 (A7), U4.32 (A7)
SDRAM_A8: U3.33 (A8), U4.33 (A8)
SDRAM_A9: U3.34 (A9), U4.34 (A9)
SDRAM_A10: U3.22 (A10/AP), U4.22 (A10/AP)
SDRAM_A11: U3.35 (A11), U4.35 (A11)
SDRAM_BA0: U3.20 (BA0), U4.20 (BA0)
SDRAM_BA1: U3.21 (BA1), U4.21 (BA1)
SDRAM_CAS_N: U3.17 (~CAS), U4.17 (~CAS)
SDRAM_CKE: U3.37 (CKE), U4.37 (CKE)
SDRAM_CLK: U3.38 (CLK), U4.38 (CLK)
SDRAM_CS_N: U3.19 (~CS), U4.19 (~CS)
SDRAM_DQM0: U3.15 (LDQM)
SDRAM_DQM1: U3.39 (UDQM)
SDRAM_DQM2: U4.15 (LDQM)
SDRAM_DQM3: U4.39 (UDQM)
SDRAM_RAS_N: U3.18 (~RAS), U4.18 (~RAS)
SDRAM_WE_N: U3.16 (~WE), U4.16 (~WE)
