badaboombox/SS-Handheld-Console/hardware/Comp Board/USB_Con.kicad_sch

## KiCad design hardware/Comp Board/USB_Con.kicad_sch (2026-07-28)

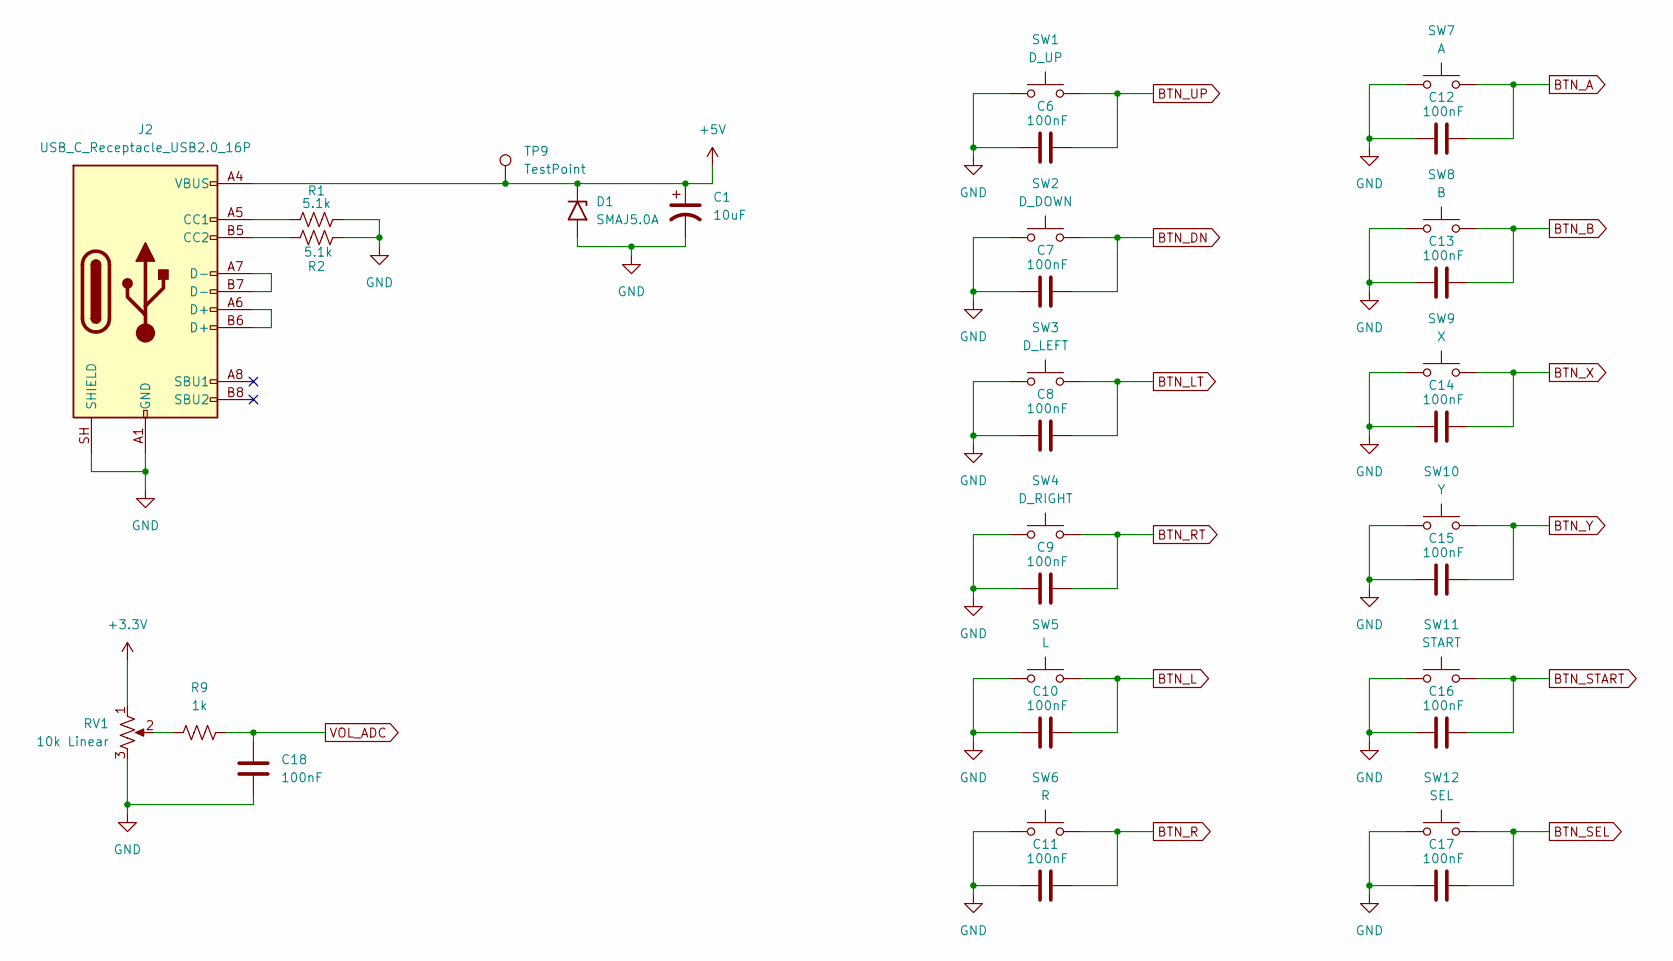
[picture p33: schematic USB_Con.kicad_sch]

Parts:
C1: 10uF; C_0805_2012Metric
C6, C7, C8, C9, C10, C11, C12, C13, C14, C15, C16, C17, C18: 100nF; C_0402_1005Metric
D1: SMAJ5.0A; D_SMA
J2: USB_C_Receptacle_USB2.0_16P; USB_C_Receptacle_G-Switch_GT-USB-7010ASV
R1, R2: 5.1k; R_0402_1005Metric
R9: 1k; R_0402_1005Metric
RV1: 10k Linear; Potentiometer_Bourns_3266Y_Vertical
SW1: D_UP; SW_SPST_EVQP2_ShortPushTravel_H2.5mm
SW2: D_DOWN; SW_SPST_EVQP2_ShortPushTravel_H2.5mm
SW3: D_LEFT; SW_SPST_EVQP2_ShortPushTravel_H2.5mm
SW4: D_RIGHT; SW_SPST_EVQP2_ShortPushTravel_H2.5mm
SW5: L; SW_Tactile_SPST_Angled_PTS645Vx39-2LFS
SW6: R; SW_Tactile_SPST_Angled_PTS645Vx39-2LFS
SW7: A; SW_SPST_EVQP2_ShortPushTravel_H2.5mm
SW8: B; SW_SPST_EVQP2_ShortPushTravel_H2.5mm
SW9: X; SW_SPST_EVQP2_ShortPushTravel_H2.5mm
SW10: Y; SW_SPST_EVQP2_ShortPushTravel_H2.5mm
SW11: START; SW_TH_Tactile_Omron_B3F-100x
SW12: SEL; SW_TH_Tactile_Omron_B3F-100x
TP9: TestPoint; TestPoint_Pad_1.5x1.5mm

Connections:
+3.3V: RV1.1
+5V: C1.1, D1.1 (A1), J2.A4 (VBUS), J2.A9 (VBUS), J2.B4 (VBUS), J2.B9 (VBUS), TP9.1
BTN_A: C12.2, SW7.2
BTN_B: C13.2, SW8.2
BTN_DN: C7.2, SW2.2
BTN_L: C10.2, SW5.2
BTN_LT: C8.2, SW3.2
BTN_R: C11.2, SW6.2
BTN_RT: C9.2, SW4.2
BTN_SEL: C17.2, SW12.2
BTN_START: C16.2, SW11.2
BTN_UP: C6.2, SW1.2
BTN_X: C14.2, SW9.2
BTN_Y: C15.2, SW10.2
GND: C1.2, C6.1, C7.1, C8.1, C9.1, C10.1, C11.1, C12.1, C13.1, C14.1, C15.1, C16.1, C17.1, C18.1, D1.2 (A2), J2.A1 (GND), J2.A12 (GND), J2.B1 (GND), J2.B12 (GND), J2.SH (SHIELD), R1.2, R2.2, RV1.3, SW1.1, SW2.1, SW3.1, SW4.1, SW5.1, SW6.1, SW7.1, SW8.1, SW9.1, SW10.1, SW11.1, SW12.1
unnamed: J2.A5 (CC1), R1.1
unnamed: J2.A6 (D+), J2.B6 (D+)
unnamed: J2.A7 (D-), J2.B7 (D-)
unnamed: J2.B5 (CC2), R2.1
unnamed: R9.1, RV1.2
VOL_ADC: C18.2, R9.2
